whatnick/Tph_Synth_Featherwing/doc/manf_log/aisler_r0.1.JPG

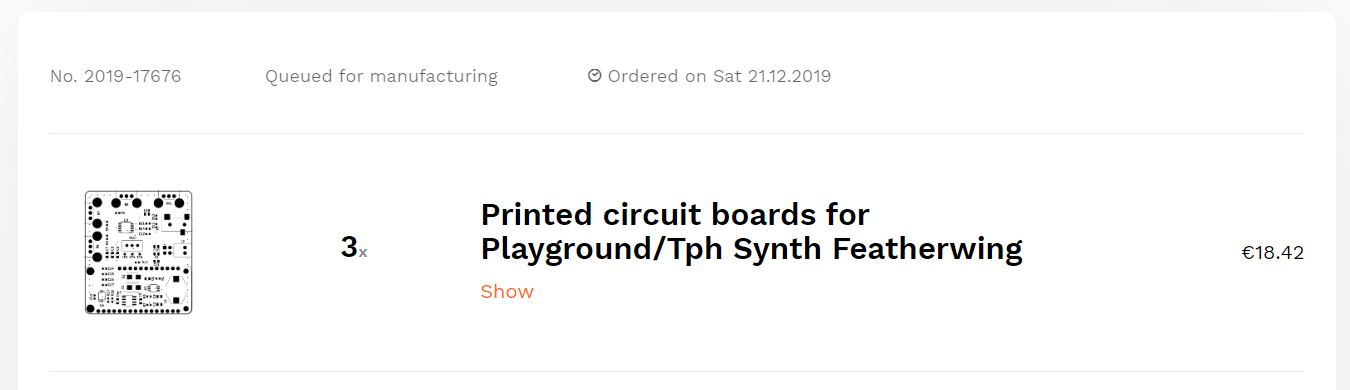
doc/manf_log/aisler_r0.1.JPG
