whatnick/Tph_Synth_Featherwing/doc/mcp4728_devkit.jpg

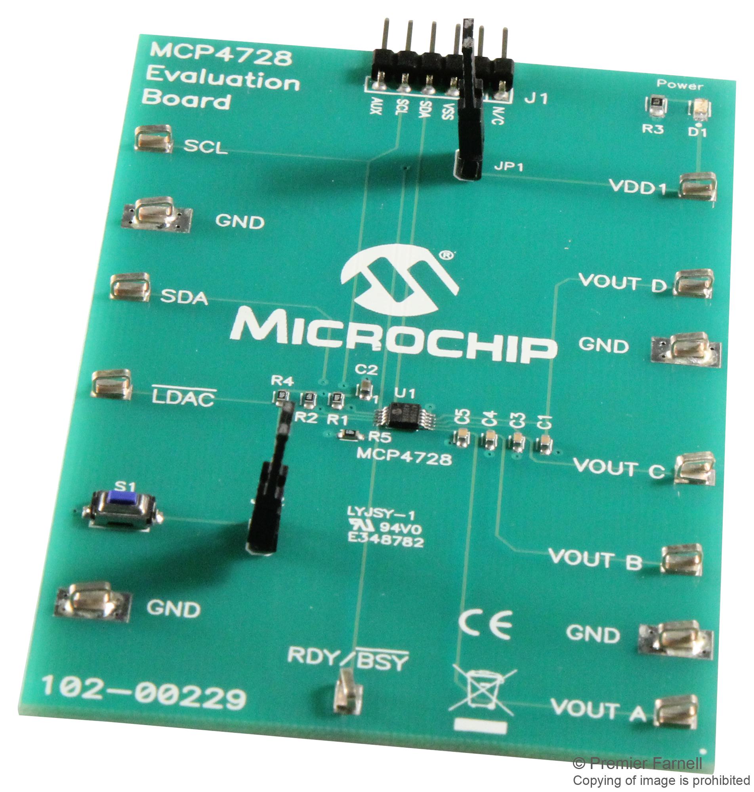
doc/mcp4728_devkit.jpg
