whatnick/Tph_Synth_Featherwing/Tph_Synth_Featherwing/plot/Tph_Synth_Featherwing-Back.png

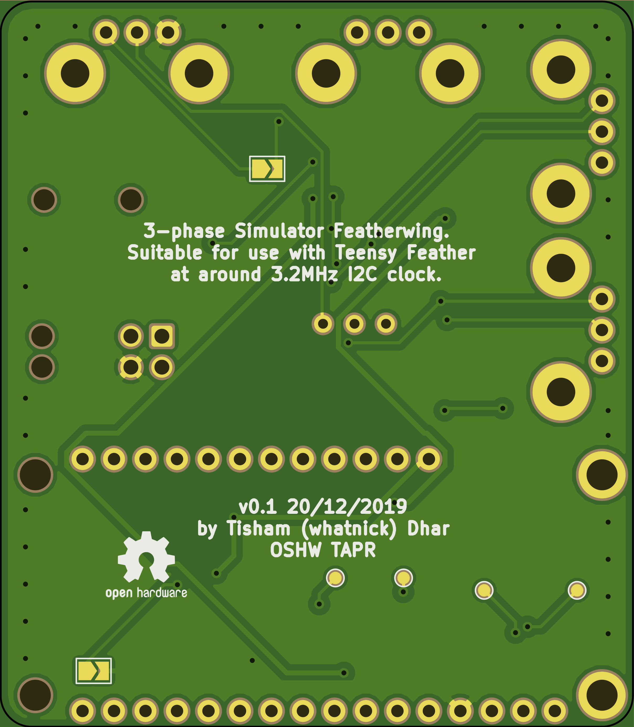
Tph_Synth_Featherwing/plot/Tph_Synth_Featherwing-Back.png
