whatnick/Tph_Synth_Featherwing/Tph_Synth_Featherwing/plot/Tph_Synth_Featherwing-Front.png

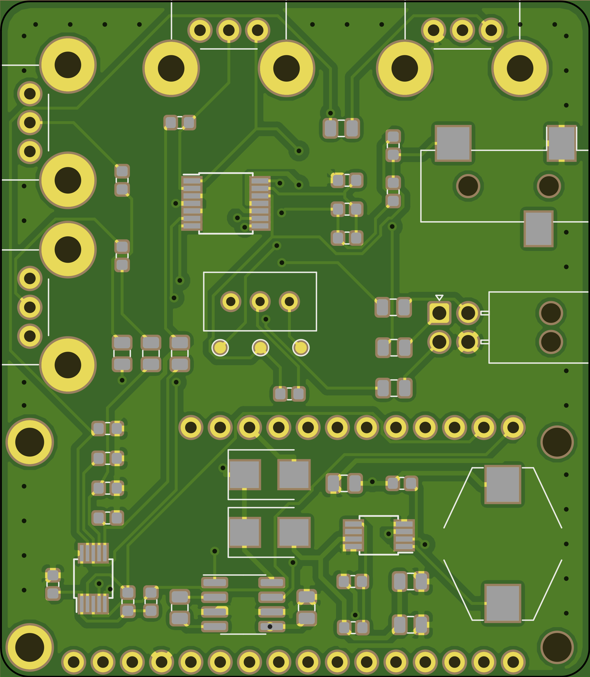
Tph_Synth_Featherwing/plot/Tph_Synth_Featherwing-Front.png
